riyassadiq11/STM32_Bluetooth_Hardware_Design_PCB/PCB_Top_Layer_(Img_Pdf_3D)/Top_Layer_Without_SilkScreen.png

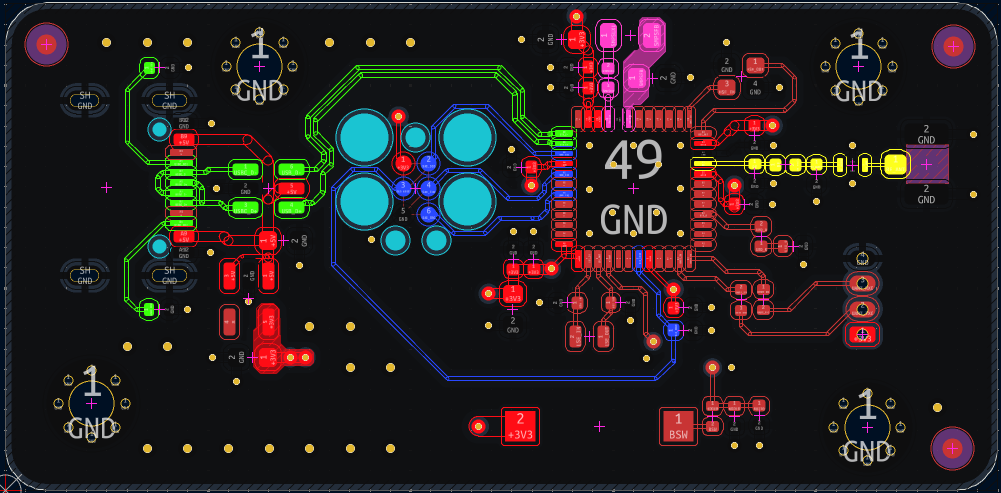
PCB_Top_Layer_(Img_Pdf_3D)/Top_Layer_Without_SilkScreen.png
